gotling/water-gate/watergate-arduino/sensor.h

#ifndef SENSOR_H
#define SENSOR_H

#include <Arduino.h>

#include "globals.h"

// DHT temperature and humidity
#define DHTTYPE DHT22

#define SENSOR_INTERVAL 10000
#define HYGRO_WARMUP_TIME 2000

void primeHygro(bool state);
float hygToPercentage(short value);
void readHygro();
void readTempHum();
void readVoltage();
void setupSensor();
bool readSensor();

#endif
