gotling/water-gate/watergate-arduino/time_functions.h

#ifndef TIME_FUNCTIONS_H
#define TIME_FUNCTIONS_H

#include <Arduino.h>
#include "RTClib.h"

// Sleep
#define TIME_TO_SLEEP 3600  // 1 hour
#define WAKE_TIME_SHORT 30 // In seconds, when just measuring
#define WAKE_TIME_LONG 60 // In seconds, when just measuring
#define WAKE_TIME_AFTER_EMPTY 60 // In seconds, when watering
#define AUTO_WATER_FAIL_SAFE 24 // Water if started from timer this many times without watering

extern RTC_DS3231 rtc;
RTC_DATA_ATTR extern short waterFailSafe;
RTC_DATA_ATTR extern int bootCount;

void time_sync_notification_cb(struct timeval *tv);
bool check_wakeup_reason();
int secondsTillNextHour();
void printLocalTime();
short getHour();
short getWeekDay();
unsigned long getEpochTime();
void setupTime();
void setupRTC();

#endif
